morgankenyon/OpenDataDisc/software/examples/16_try_avalonia/README.md

# Avalonia Getting Started

Getting to know Avalonia UI library, probably going to be what I build my desktop app off of.

Currently I'm just playing with the tutorial. In a future example I will spin this off into a Application that I can interact with my microcontroller.

## Resources

* Avalonia Extensions - https://marketplace.visualstudio.com/items?itemName=AvaloniaTeam.AvaloniaVS
* Music Store Sample App - https://docs.avaloniaui.net/docs/tutorials/music-store-app/creating-the-project
