morgankenyon/OpenDataDisc/software/examples/10_accelerometer_angles/README.md

# Accelerometer Angles

This example will help me measure angles from my MPU 6050.

This will mainly pull from this [youtube video](https://www.youtube.com/watch?v=7VW_XVbtu9k&t=596s).

I've done a lot of bluetooth with my latest software examples, but in this one I'm going to just be using serial to communicate with my esp32. Basically just simplifying the example to get it working.

## Esp32

* Upload to board
  * `pio run --target upload`
