morgankenyon/OpenDataDisc/software/examples/04_bluetooth_esp32_to_windows/image-5.png

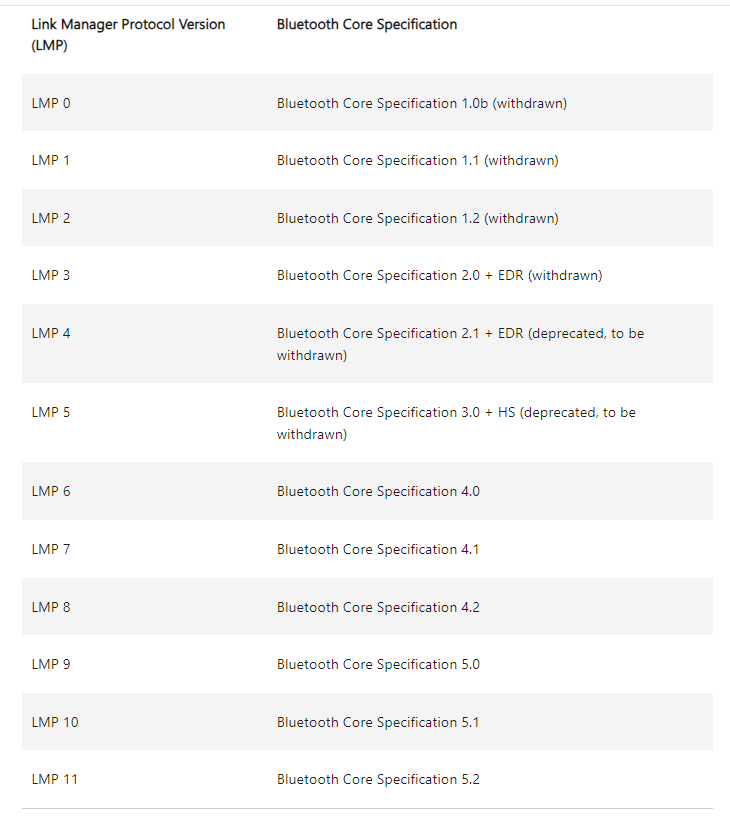
software/examples/04_bluetooth_esp32_to_windows/image-5.png
