morgankenyon/OpenDataDisc/software/examples/22_wsn_iot_tutorials/ble_battery_service/src/main.c

#include <zephyr/kernel.h>
#include <zephyr/logging/log.h>

#include <zephyr/bluetooth/bluetooth.h>
#include <zephyr/bluetooth/conn.h>
#include <zephyr/bluetooth/gatt.h>
#include <zephyr/bluetooth/uuid.h>
#include <zephyr/bluetooth/services/bas.h>

LOG_MODULE_REGISTER(ble_bas);

volatile bool ble_ready=false;
uint8_t battery_level=100;

static const struct bt_data ad[] = 
{
	BT_DATA_BYTES(BT_DATA_FLAGS, (BT_LE_AD_GENERAL | BT_LE_AD_NO_BREDR)),
	BT_DATA_BYTES(BT_DATA_UUID16_ALL, BT_UUID_16_ENCODE(BT_UUID_BAS_VAL))
};

void bt_ready(int err)
{
	if (err)
	{
		LOG_ERR("bt enable returns %d", err);
	}

	LOG_INF("bt_ready!\n");
	ble_ready = true;
}

int init_ble(void)
{
	LOG_INF("Init BLE");
	int err;

	LOG_INF("AfterInit BLE");
	//bt_conn_cb_register(&conn_callbacks);

	err = bt_enable(bt_ready);
	
	LOG_INF("After bt_enable");
	if (err)
	{
		LOG_INF("Also an error");
		LOG_ERR("bt_enable failed (err %d)", err);
		return err;
	}

	
	LOG_INF("returning");

	return 0;
}

int main(void)
{
	printk("Hello world! %s\n", CONFIG_BOARD);
	init_ble();

	while (!ble_ready)
	{
		LOG_INF("BLE stack not ready yet");
		k_msleep(100);
	}
	LOG_INF("BLE stack ready");

	int err;
	err = bt_le_adv_start(BT_LE_ADV_CONN_NAME, ad, ARRAY_SIZE(ad), NULL, 0);
	if (err)
	{
		printk("Advertising failed to start (err %d)\n", err);
		return 1;
	}

	while (true)
	{
		k_msleep(2000);

		if (battery_level < 25)
		{
			battery_level = 100;
		}
		else
		{
			battery_level--;
		}

		bt_bas_set_battery_level(battery_level);

		printk("Hello world! %s\n", CONFIG_BOARD);
	}
	//printk("Hello world! %s\n", CONFIG_BOARD);

	return 0;
}
