morgankenyon/OpenDataDisc/software/examples/13_nrf52_imu_platformio/nrf52/src/main.cpp

/*****************************************************************************/
//Code taken from Arduino example, now trying to use it in platformIO
/*******************************************************************************/

#include "Arduino.h"
#include "LSM6DS3.h"
#include "Wire.h"

//Create a instance of class LSM6DS3
LSM6DS3 myIMU(I2C_MODE, 0x6A);    //I2C device address 0x6A


void setup() {
    pinMode(LED_BUILTIN, OUTPUT);
    // put your setup code here, to run once:
    Serial.begin(115200);
    while (!Serial);
    //Call .begin() to configure the IMUs
    if (myIMU.begin() != 0) {
        Serial.println("Device error");
    } else {
        Serial.println("Device OK!");
    }
}

void loop() {
    //Accelerometer
    Serial.print("\nAccelerometer:\n");
    Serial.print(" X1 = ");
    Serial.println(myIMU.readFloatAccelX(), 4);
    Serial.print(" Y1 = ");
    Serial.println(myIMU.readFloatAccelY(), 4);
    Serial.print(" Z1 = ");
    Serial.println(myIMU.readFloatAccelZ(), 4);

    //Gyroscope
    Serial.print("\nGyroscope:\n");
    Serial.print(" X1 = ");
    Serial.println(myIMU.readFloatGyroX(), 4);
    Serial.print(" Y1 = ");
    Serial.println(myIMU.readFloatGyroY(), 4);
    Serial.print(" Z1 = ");
    Serial.println(myIMU.readFloatGyroZ(), 4);

    //Thermometer
    Serial.print("\nThermometer:\n");
    Serial.print(" Degrees C1 = ");
    Serial.println(myIMU.readTempC(), 4);
    Serial.print(" Degrees F1 = ");
    Serial.println(myIMU.readTempF(), 4);

    digitalWrite(LED_BUILTIN, HIGH);
    delay(1000);
    digitalWrite(LED_BUILTIN, LOW);

    delay(1000);
}
