morgankenyon/OpenDataDisc/software/examples/05_platform_io/esp32/src/main.cpp

/**
 * Blink
 *
 * Turns on an LED on for one second,
 * then off for one second, repeatedly.
 */
#include "Arduino.h"

#ifndef LED_BUILTIN
#define LED_BUILTIN 13
#endif

void setup()
{
  Serial.begin(115200);
  // initialize LED digital pin as an output.
  pinMode(LED_BUILTIN, OUTPUT);
}

void loop()
{
  // turn the LED on (HIGH is the voltage level)
  digitalWrite(LED_BUILTIN, HIGH);

  // wait for a second
  delay(1000);

  // turn the LED off by making the voltage LOW
  digitalWrite(LED_BUILTIN, LOW);

   // wait for a second
  delay(1000);

  Serial.println("Looping again!!");
}
